adriel-babalola/oa_usb_hub/pcb/image-5.png

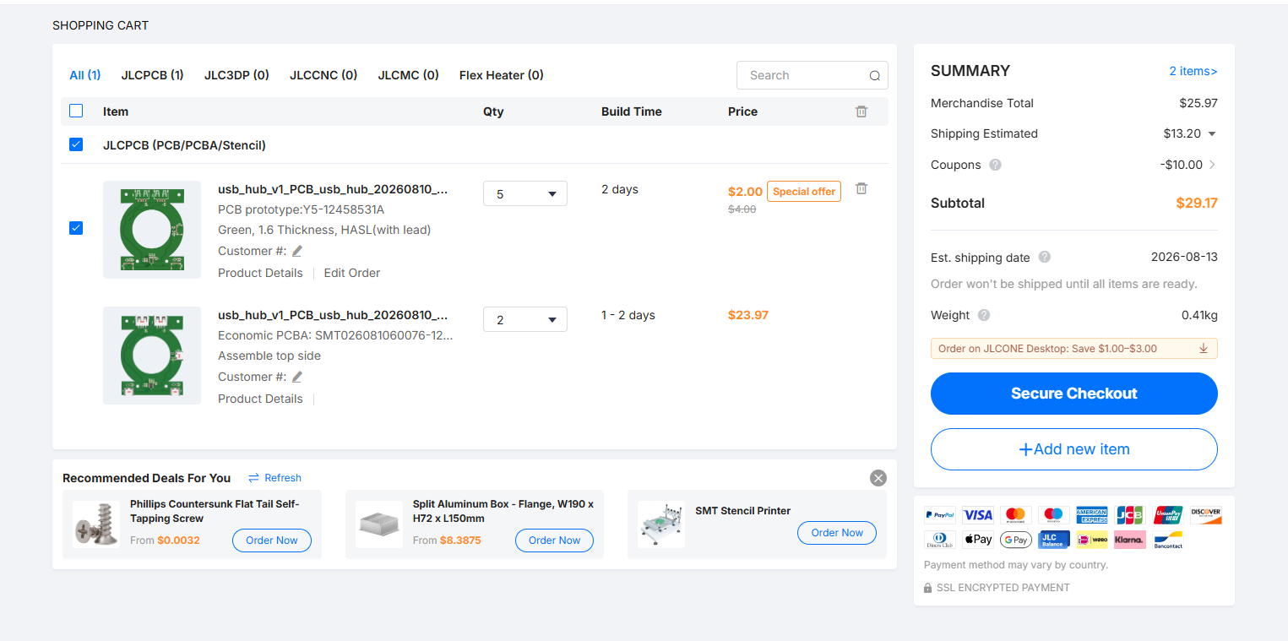
pcb/image-5.png
